antoinejulien/Level-US_GRO400_H21/Mechanics/CAD_prototype_2/bras_2.SLDPRT

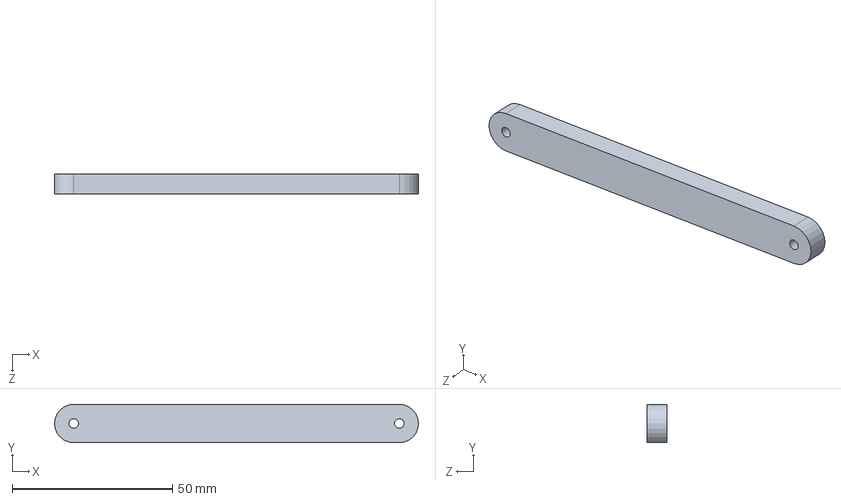
[picture p22: CAD file, 2021-02-21]
Mechanics/CAD_prototype_2/bras_2.SLDPRT
113.6 x 12.0 x 6.35 mm
