antoinejulien/Level-US_GRO400_H21/Mechanics/CAD_prototype_2/bras_3.SLDPRT

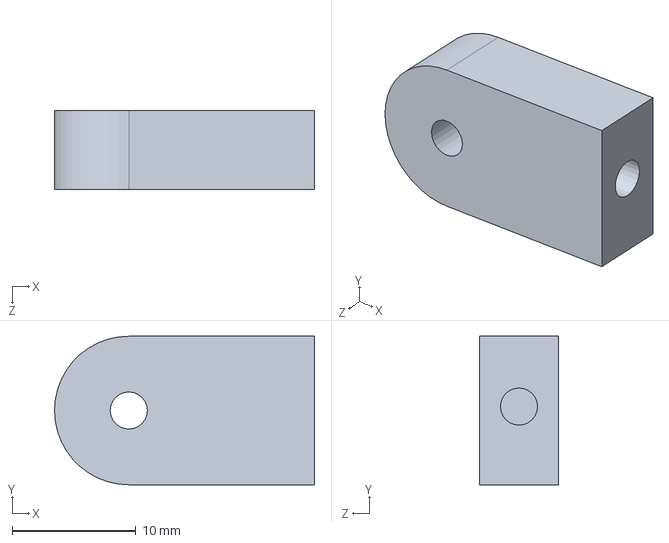
[picture p23: CAD file, 2021-02-21]
Mechanics/CAD_prototype_2/bras_3.SLDPRT
21.0 x 12.0 x 6.35 mm
