antoinejulien/Level-US_GRO400_H21/Mechanics/Prototype finale/Fixation Shaft.SLDPRT

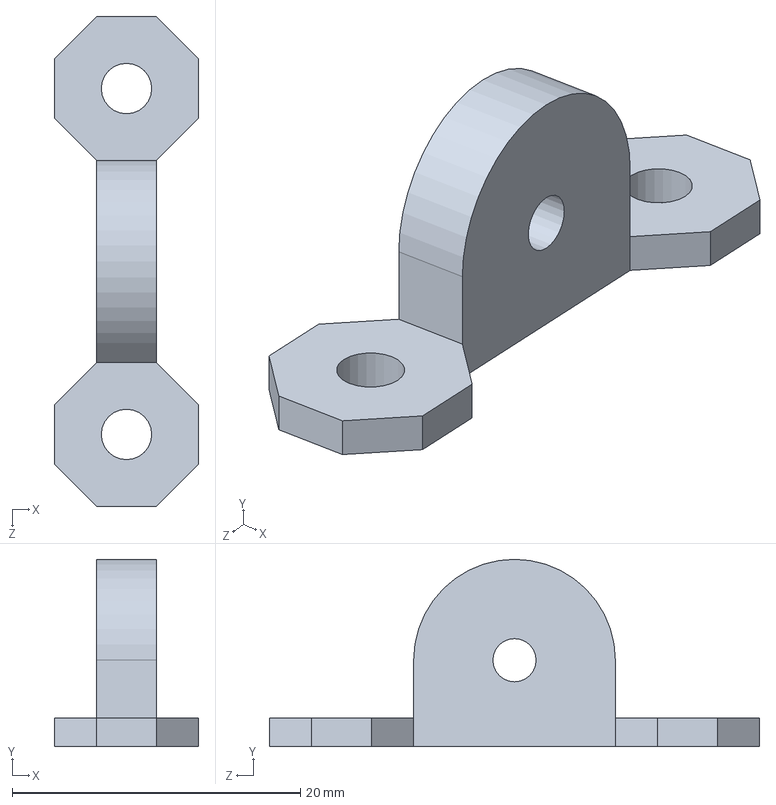
[picture p24: CAD file, 2021-04-14]
Mechanics/Prototype finale/Fixation Shaft.SLDPRT
10.0 x 13.0 x 34.0 mm
