antoinejulien/Level-US_GRO400_H21/Mechanics/CAD_prototype_2/Arbre.SLDPRT

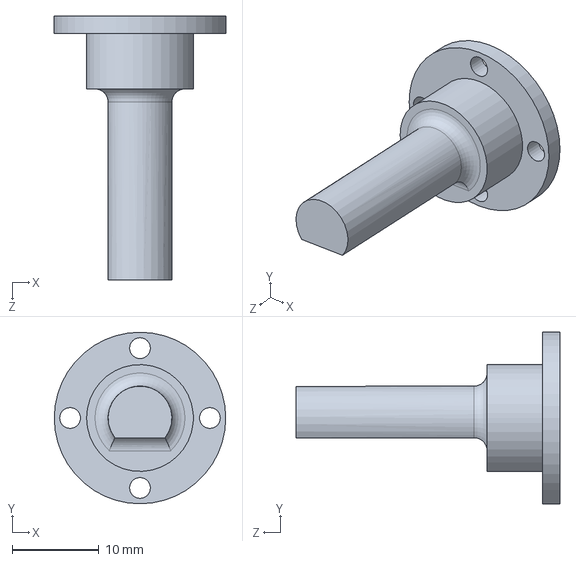
[picture p25: CAD file, 2021-02-21]
Mechanics/CAD_prototype_2/Arbre.SLDPRT
19.8 x 19.8 x 30.4 mm
