antoinejulien/Level-US_GRO400_H21/Mechanics/Prototype finale/Bras 1.SLDPRT

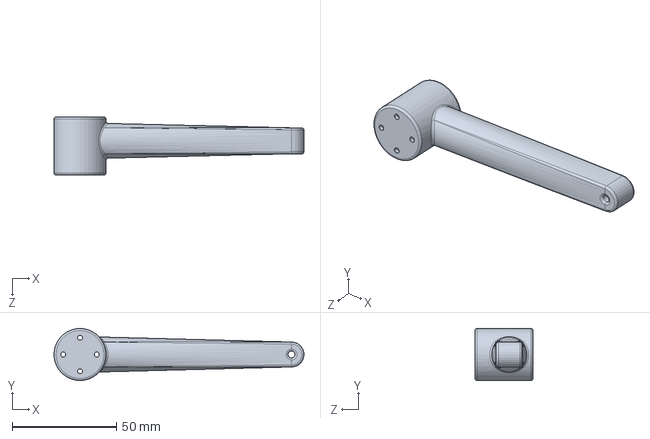
[picture p26: CAD file, 2021-04-14]
Mechanics/Prototype finale/Bras 1.SLDPRT
120.1 x 25.0 x 28.0 mm
