antoinejulien/Level-US_GRO400_H21/Mechanics/Prototype finale/Bras 2.SLDPRT

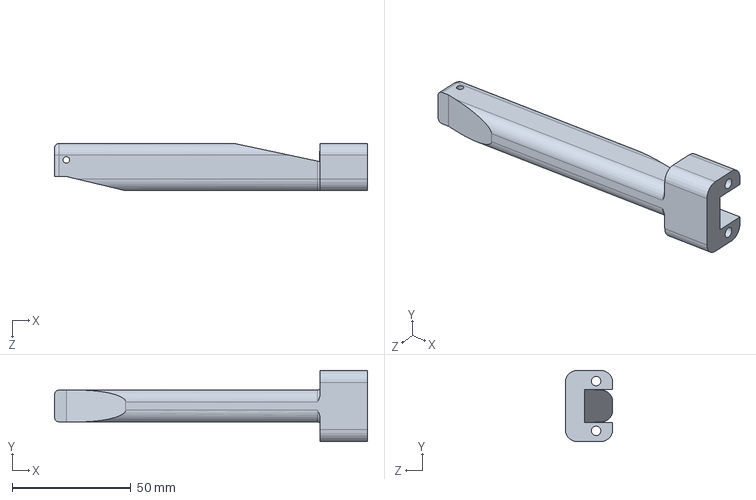
[picture p27: CAD file, 2021-04-14]
Mechanics/Prototype finale/Bras 2.SLDPRT
132.0 x 30.0 x 20.0 mm
