antoinejulien/Level-US_GRO400_H21/Mechanics/Prototype finale/Shaft.SLDPRT

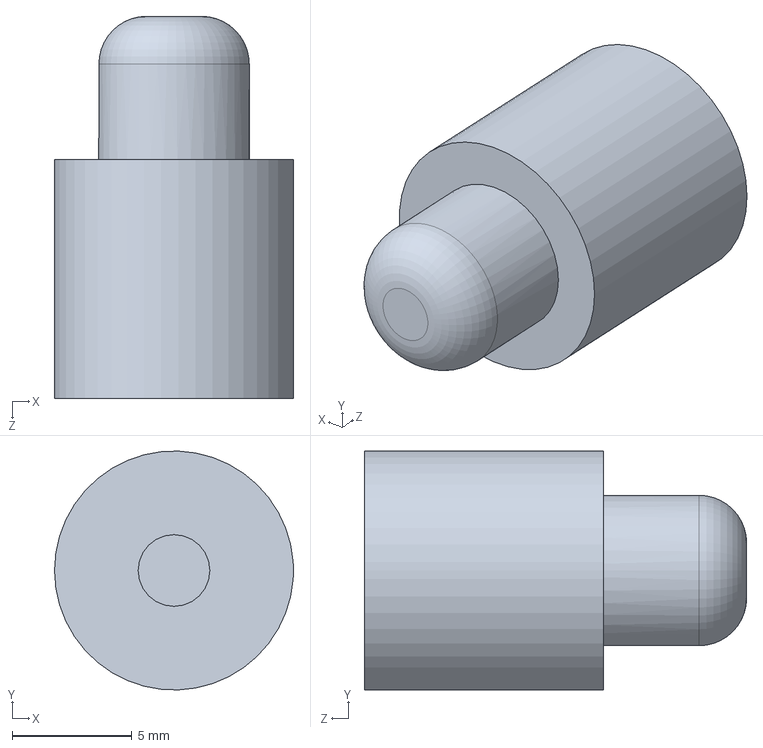
[picture p28: CAD file, 2021-04-14]
Mechanics/Prototype finale/Shaft.SLDPRT
10.0 x 9.99 x 16.0 mm
