antoinejulien/Level-US_GRO400_H21/Mechanics/Prototype finale/Bearing.SLDPRT

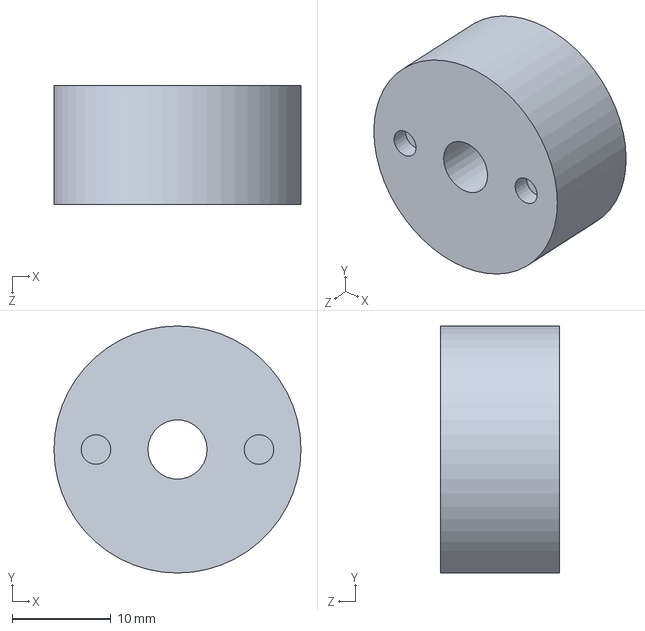
[picture p29: CAD file, 2021-04-14]
Mechanics/Prototype finale/Bearing.SLDPRT
25.0 x 25.0 x 12.0 mm
