antoinejulien/Level-US_GRO400_H21/Mechanics/Prototype finale/Base.SLDPRT

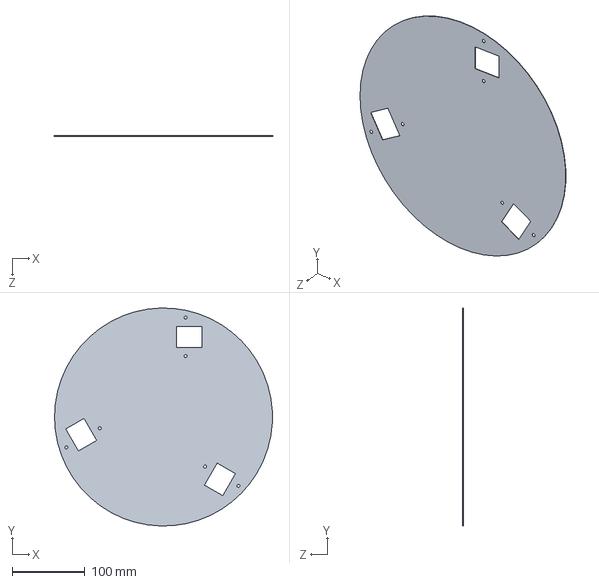
[picture p30: CAD file, 2021-04-14]
Mechanics/Prototype finale/Base.SLDPRT
300.0 x 299.9 x 0.5 mm
