antoinejulien/Level-US_GRO400_H21/Mechanics/Prototype finale/OpenCR.SLDPRT

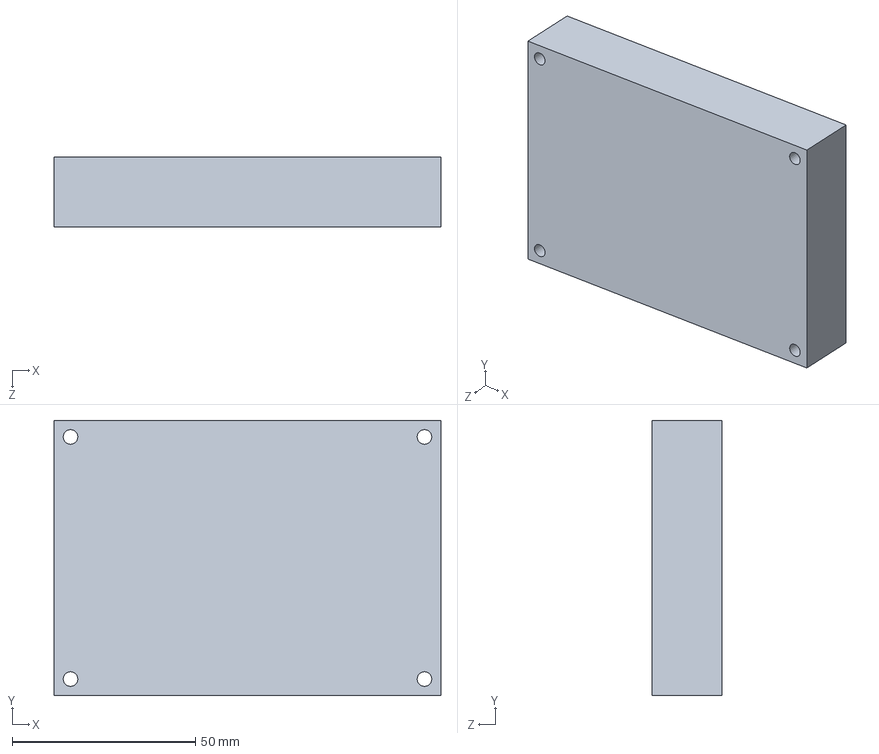
[picture p31: CAD file, 2021-02-21]
Mechanics/Prototype finale/OpenCR.SLDPRT
105.5 x 75.0 x 19.0 mm
